RikkOmsk/KegScale/3dModel/log02_im1.png

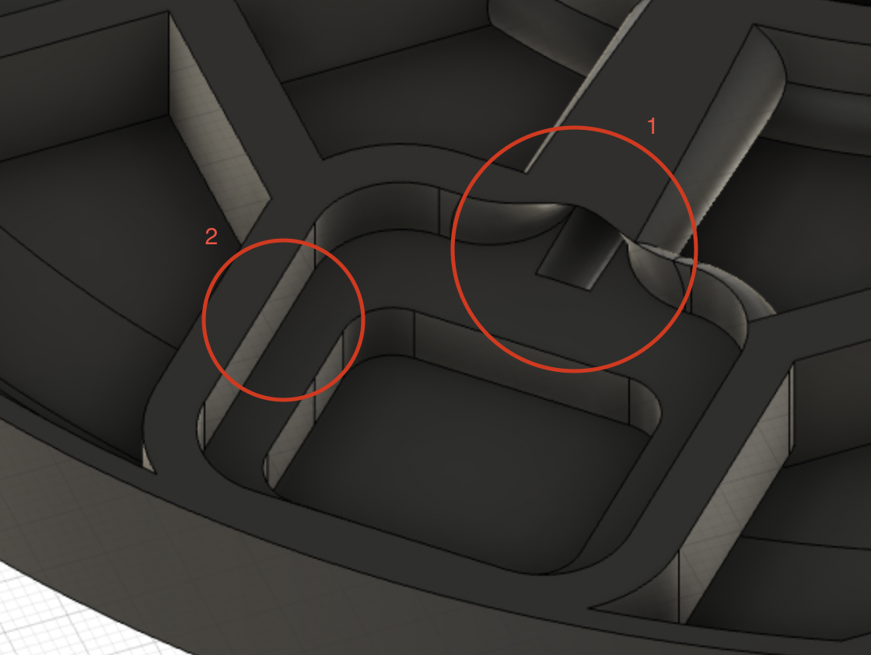
3dModel/log02_im1.png
