RikkOmsk/KegScale/3dModel/log02_im2.png

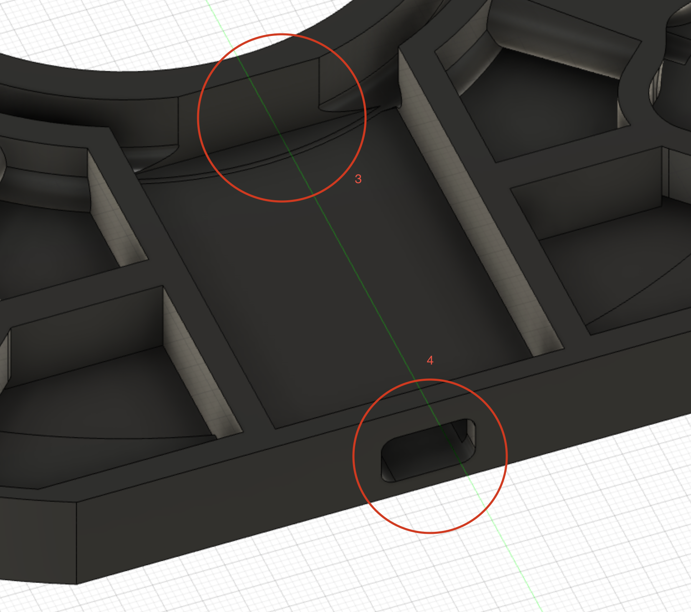
3dModel/log02_im2.png
